Quee0/SimpleOverdriveGuitarEffect/img/import/flame.png

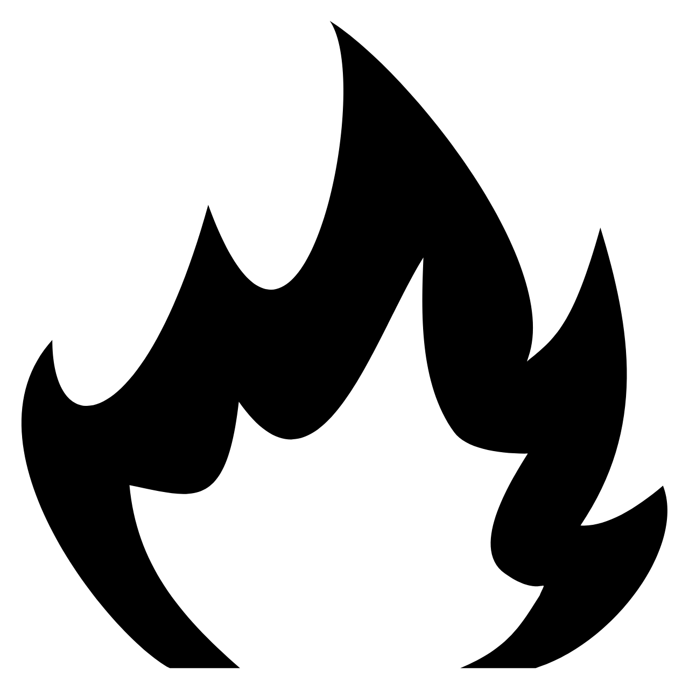
img/import/flame.png
