Quee0/SimpleOverdriveGuitarEffect/img/import/flames_binar.png

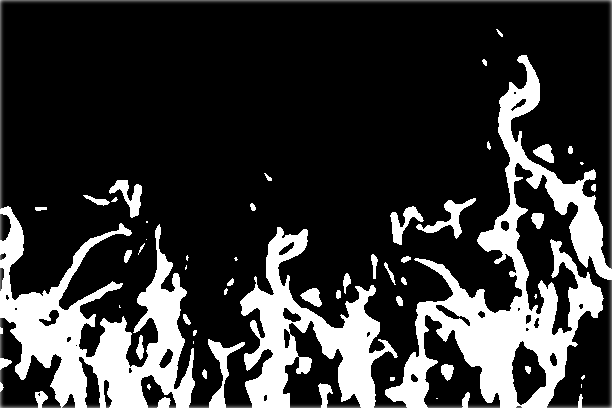
img/import/flames_binar.png
