Quee0/SimpleOverdriveGuitarEffect/img/import/guitar.png

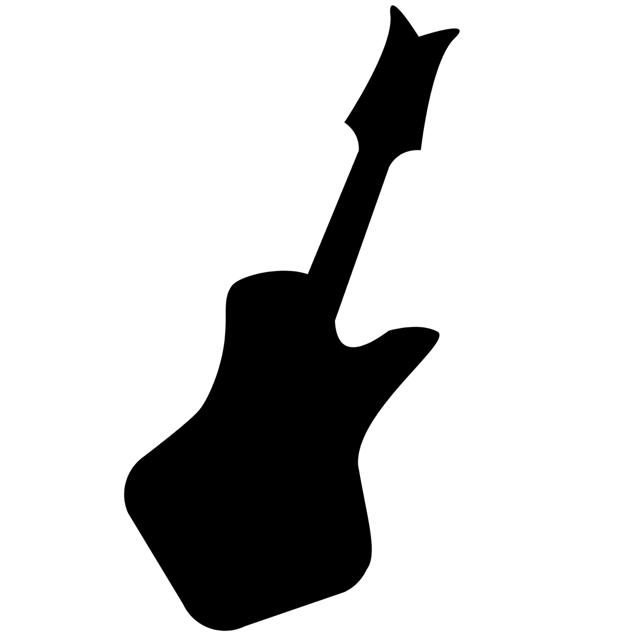
img/import/guitar.png
