Quee0/SimpleOverdriveGuitarEffect/model/import/M12 NUT FOR FOOTSWITCH.STEP

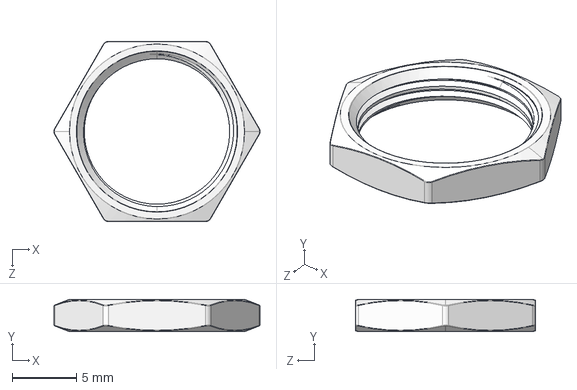
[picture p42: CAD file, 2026-05-04]
model/import/M12 NUT FOR FOOTSWITCH.STEP
16.0 x 2.50 x 14.0 mm
