Quee0/SimpleOverdriveGuitarEffect/model/import/M7 × 0.75 NUT.STEP

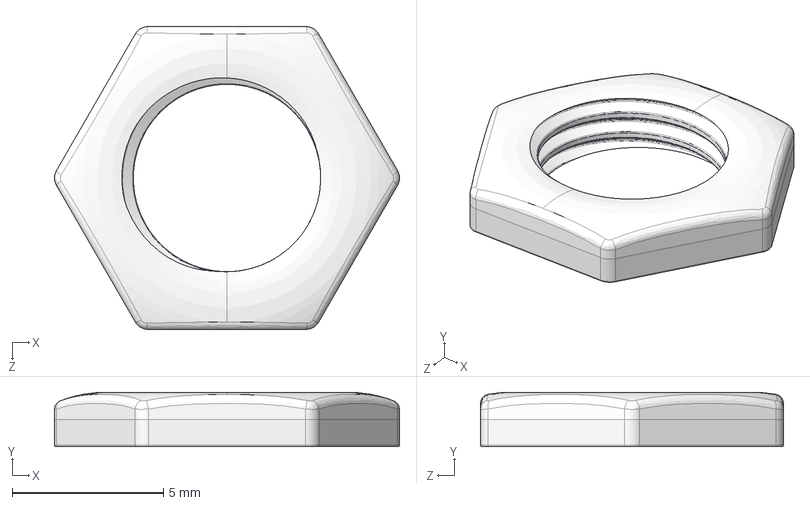
[picture p43: CAD file, 2026-05-04]
model/import/M7 × 0.75 NUT.STEP
11.4 x 1.80 x 10.0 mm
