Quee0/SimpleOverdriveGuitarEffect/model/import/Push_Button_Nut.STEP

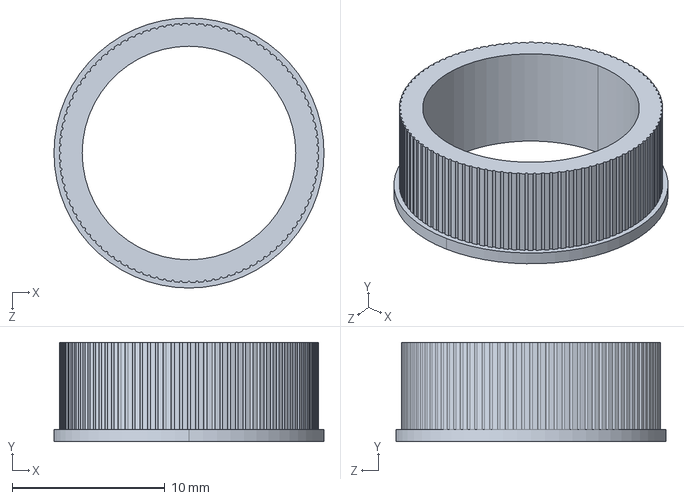
[picture p44: CAD file, 2026-04-05]
model/import/Push_Button_Nut.STEP
17.7 x 6.50 x 17.7 mm
